hfxbse/SportBuzzer/SportBuzzer.ino

/*
 * DON'T USE THIS FILE! THIS WOULD BREAK THE CMAKE COMPATIBILITY!
 *
 * This file only purpose is to make the project compile in the Arduino IDE
 * The actual starting point is the file "SportBuzzer.cpp"
 */
