hfxbse/SportBuzzer/src/HardwareInterfaces/HC12_Options.hpp

//
// Created by stubit on 4/13/20.
//

#pragma clang diagnostic push
#pragma ide diagnostic ignored "UnusedGlobalDeclarationInspection"

#ifndef SPORTBUZZER_HC12_OPTIONS_HPP
#define SPORTBUZZER_HC12_OPTIONS_HPP


enum Baud {     // available baud rates. Higher baud rate reduces the range in which the module works
    B1200 = 1200,
    B2400 = 2400,
    B4800 = 4800,
    B9600 = 9600,
    B19200 = 19200,
    B38400 = 38400,
    B57600 = 57600,
    B115200 = 115200
};

enum Channel {  // available channel, each 400KHz higher
    C001 = 1,
    C002 = 2,
    C003 = 3,
    C004 = 4,
    C005 = 5,
    C006 = 6,
    C007 = 7,
    C008 = 8,
    C009 = 9,
    C010 = 10,
    C011 = 11,
    C012 = 12,
    C013 = 13,
    C014 = 14,
    C015 = 15,
    C016 = 16,
    C017 = 17,
    C018 = 18,
    C019 = 19,
    C020 = 20,
    C021 = 21,
    C022 = 22,
    C023 = 23,
    C024 = 24,
    C025 = 25,
    C026 = 26,
    C027 = 27,
    C028 = 28,
    C029 = 29,
    C030 = 30,
    C031 = 31,
    C032 = 32,
    C033 = 33,
    C034 = 34,
    C035 = 35,
    C036 = 36,
    C037 = 37,
    C038 = 38,
    C039 = 39,
    C040 = 40,
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
};

enum TransmissionPowerMode {
    P1 = 1,     // -1 dBm
    P2 = 2,     //  2 dBm
    P3 = 3,     //  5 dBm
    P4 = 4,     //  8 dBm
    P5 = 5,     // 11 dBm
    P6 = 6,     // 14 dBm
    P7 = 7,     // 17 dBm
    P8 = 8,     // 20 dBm
};

#endif //SPORTBUZZER_HC12_OPTIONS_HPP

#pragma clang diagnostic pop
