hfxbse/SportBuzzer/src/GUI/NavigationBar.hpp

//
// Created by stubit on 8/4/21.
//

#ifndef SPORTBUZZER_NAVIGATIONBAR_HPP
#define SPORTBUZZER_NAVIGATIONBAR_HPP

#include <src/HardwareInterfaces/Display.hpp>
#include "Options.hpp"
#include "src/GUI/fonts/Roboto_Medium8pt7b.h"

int16_t drawNavigationBar(Display &display, const Option *options, size_t optionCount);

#endif //SPORTBUZZER_NAVIGATIONBAR_HPP
